patr3s/-737-800-Captain-MIP/CAD/DU_bezel_v3/exports/737-MIP-001_DU-bezel-light-base_v3.stl

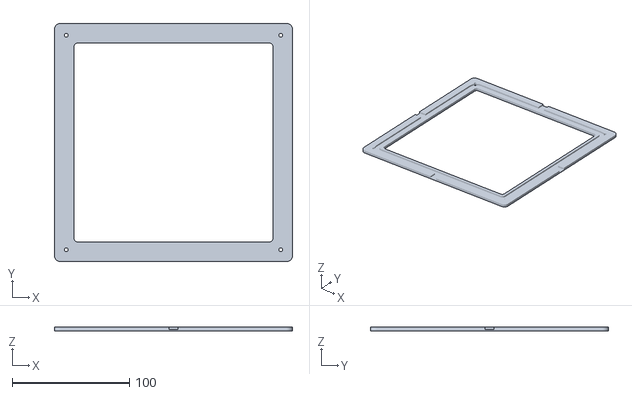
[picture p15: CAD file, 2026-08-28]
CAD/DU_bezel_v3/exports/737-MIP-001_DU-bezel-light-base_v3.stl
203.2 x 203.2 x 3.20
