patr3s/-737-800-Captain-MIP/CAD/Dual_concentric_knob_v1/exports/737-MIP-KNB-002_upper-knob_PROVISIONAL_v1.stl

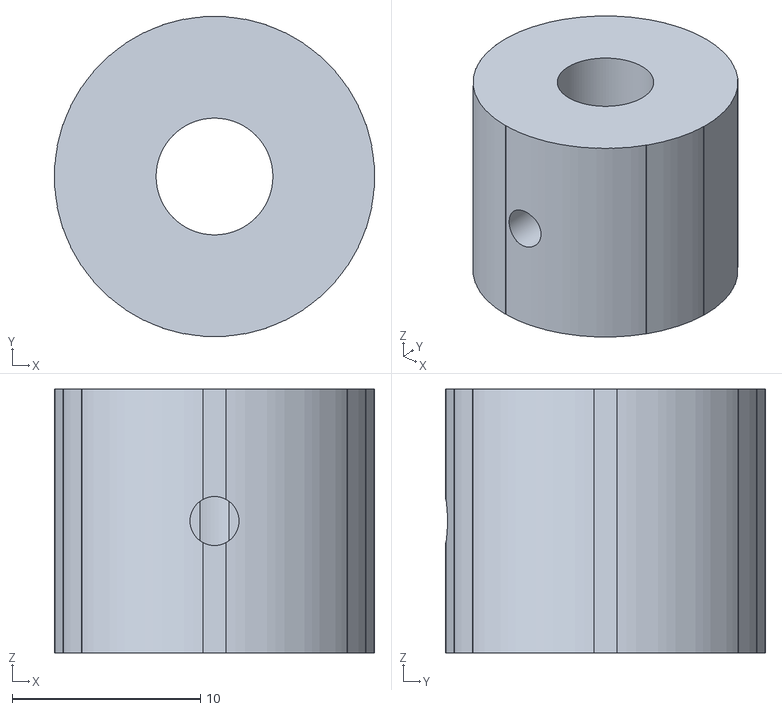
[picture p16: CAD file, 2026-08-28]
CAD/Dual_concentric_knob_v1/exports/737-MIP-KNB-002_upper-knob_PROVISIONAL_v1.stl
17.0 x 17.0 x 14.0
