patr3s/-737-800-Captain-MIP/CAD/PFD_ND_alignment_fit_check_v1/exports_v1.1/737-MIP-CAL-003B_fascia-seam-joiner_v1.1.stl

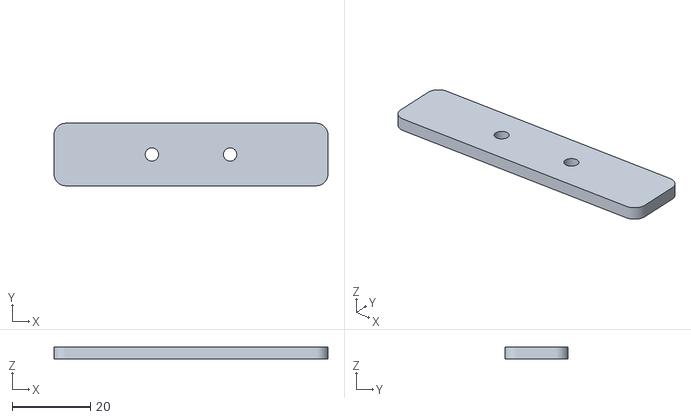
[picture p17: CAD file, 2026-09-04]
CAD/PFD_ND_alignment_fit_check_v1/exports_v1.1/737-MIP-CAL-003B_fascia-seam-joiner_v1.1.stl
70.0 x 16.0 x 3.00
