patr3s/-737-800-Captain-MIP/CAD/Steel_VESA_alignment_interface_v1/exports/737-MIP-007_xy_plate_PROVISIONAL_v1.stl

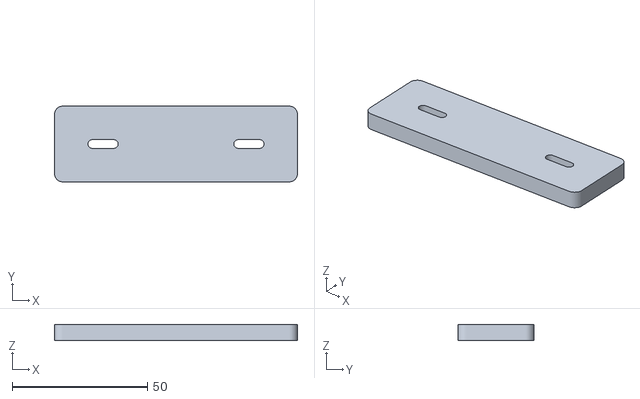
[picture p19: CAD file, 2026-08-28]
CAD/Steel_VESA_alignment_interface_v1/exports/737-MIP-007_xy_plate_PROVISIONAL_v1.stl
90.0 x 28.0 x 6.00
