patr3s/-737-800-Captain-MIP/Ready-to-Print/PFD-ND-Alignment-Fit-Check-v1/737-MIP-CAL-003_carrier_right_v1.stl

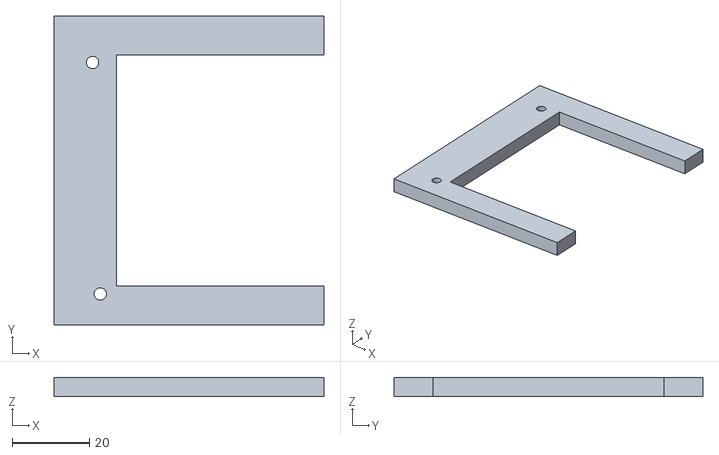
[picture p20: CAD file, 2026-08-28]
Ready-to-Print/PFD-ND-Alignment-Fit-Check-v1/737-MIP-CAL-003_carrier_right_v1.stl
70.0 x 80.0 x 5.00
