patr3s/-737-800-Captain-MIP/CAD/Backlight_test_panel_v1/exports/737-MIP-CAL-002B_backlight-diffuser_v1.1.stl

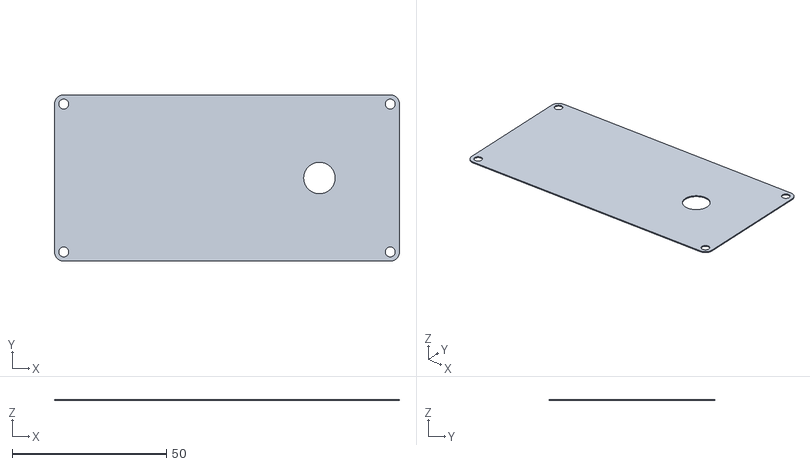
[picture p21: CAD file, 2026-08-28]
CAD/Backlight_test_panel_v1/exports/737-MIP-CAL-002B_backlight-diffuser_v1.1.stl
112.0 x 54.0 x 0.4
