patr3s/-737-800-Captain-MIP/CAD/Backlight_test_panel_v1/exports_multicolor_v1/737-MIP-CAL-004_legends-A-1.0mm.stl

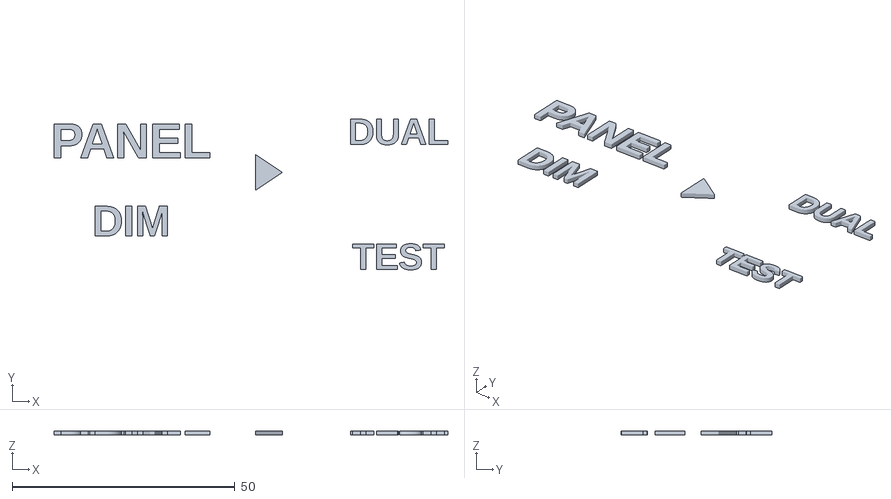
[picture p22: CAD file, 2026-09-04]
CAD/Backlight_test_panel_v1/exports_multicolor_v1/737-MIP-CAL-004_legends-A-1.0mm.stl
88.4 x 33.9 x 1.00
