patr3s/-737-800-Captain-MIP/CAD/BenQ_VESA_cradle_v1/exports/737-MIP-005_VESA-plate_v1.stl

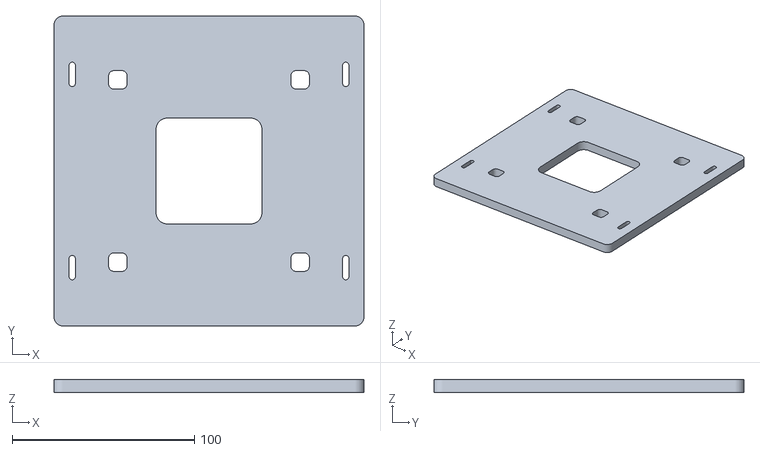
[picture p23: CAD file, 2026-08-27]
CAD/BenQ_VESA_cradle_v1/exports/737-MIP-005_VESA-plate_v1.stl
170.0 x 170.0 x 7.00
