patr3s/-737-800-Captain-MIP/CAD/PFD_ND_carrier_v1/exports/737-MIP-003A_joiner-v1.stl

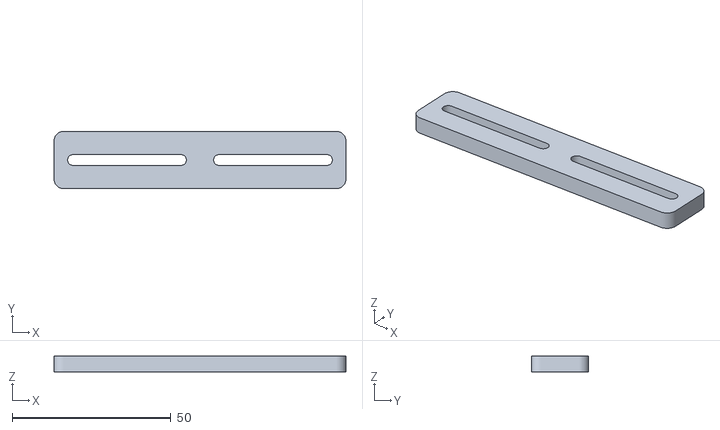
[picture p25: CAD file, 2026-08-27]
CAD/PFD_ND_carrier_v1/exports/737-MIP-003A_joiner-v1.stl
92.0 x 18.0 x 5.00
