patr3s/-737-800-Captain-MIP/CAD/Steel_VESA_alignment_interface_v1/exports/737-MIP-007_shim_20_PROVISIONAL_v1.stl

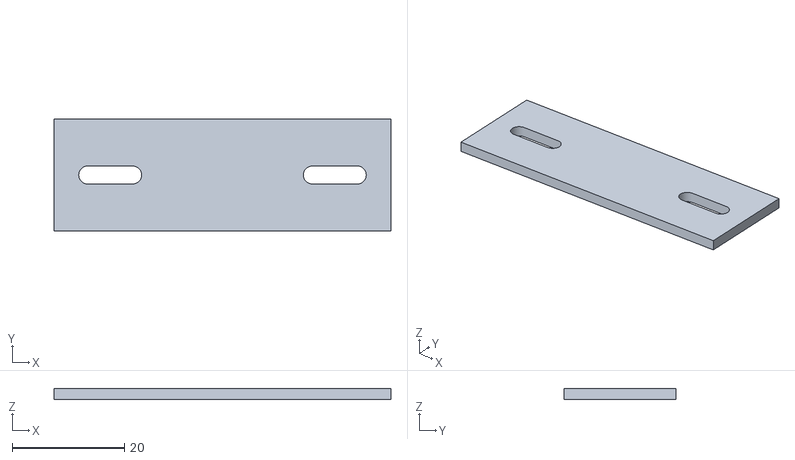
[picture p27: CAD file, 2026-08-28]
CAD/Steel_VESA_alignment_interface_v1/exports/737-MIP-007_shim_20_PROVISIONAL_v1.stl
60.0 x 20.0 x 2.00
