patr3s/-737-800-Captain-MIP/Ready-to-Print/PFD-ND-Alignment-Fit-Check-v1/737-MIP-CAL-003_fascia_seam_left_v1.stl

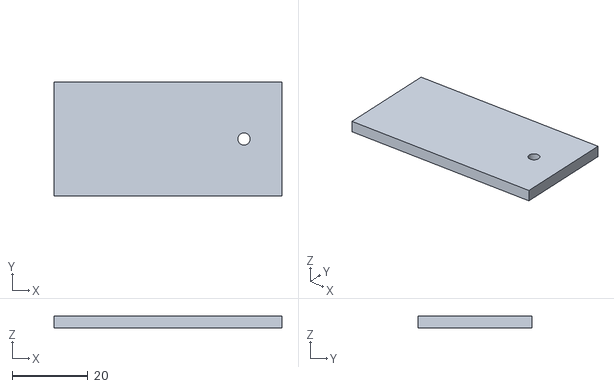
[picture p28: CAD file, 2026-08-28]
Ready-to-Print/PFD-ND-Alignment-Fit-Check-v1/737-MIP-CAL-003_fascia_seam_left_v1.stl
60.0 x 30.0 x 3.20
