patr3s/-737-800-Captain-MIP/CAD/BenQ_VESA_cradle_v1/exports/737-MIP-005A_rear-wing_v1.stl

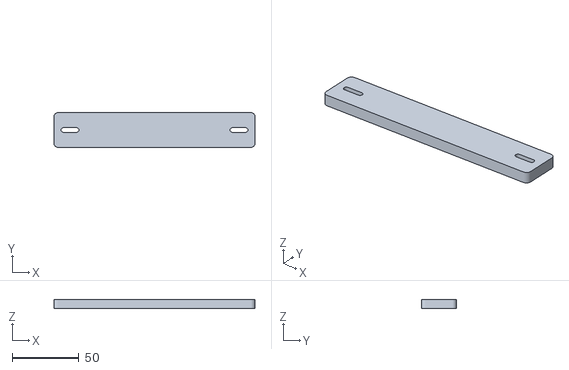
[picture p29: CAD file, 2026-08-27]
CAD/BenQ_VESA_cradle_v1/exports/737-MIP-005A_rear-wing_v1.stl
150.0 x 26.0 x 7.00
