patr3s/-737-800-Captain-MIP/CAD/PFD_ND_carrier_v1/exports/737-MIP-003B_top-interface-v1.stl

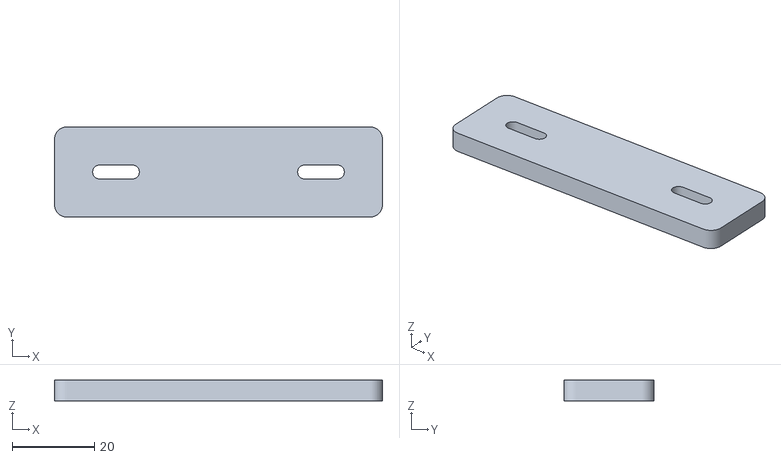
[picture p30: CAD file, 2026-08-27]
CAD/PFD_ND_carrier_v1/exports/737-MIP-003B_top-interface-v1.stl
80.0 x 22.0 x 5.00
