patr3s/-737-800-Captain-MIP/CAD/PFD_ND_fascia_v1/exports/737-MIP-006_bottom_left_base_v1.stl

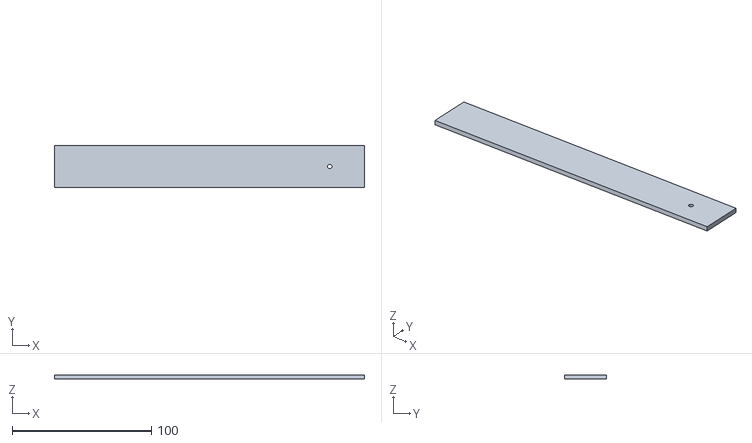
[picture p35: CAD file, 2026-08-28]
CAD/PFD_ND_fascia_v1/exports/737-MIP-006_bottom_left_base_v1.stl
222.5 x 30.2 x 3.20
