patr3s/-737-800-Captain-MIP/Ready-to-Print/PFD-ND-Alignment-Fit-Check-v1/737-MIP-CAL-003_bezel_left_v1.stl

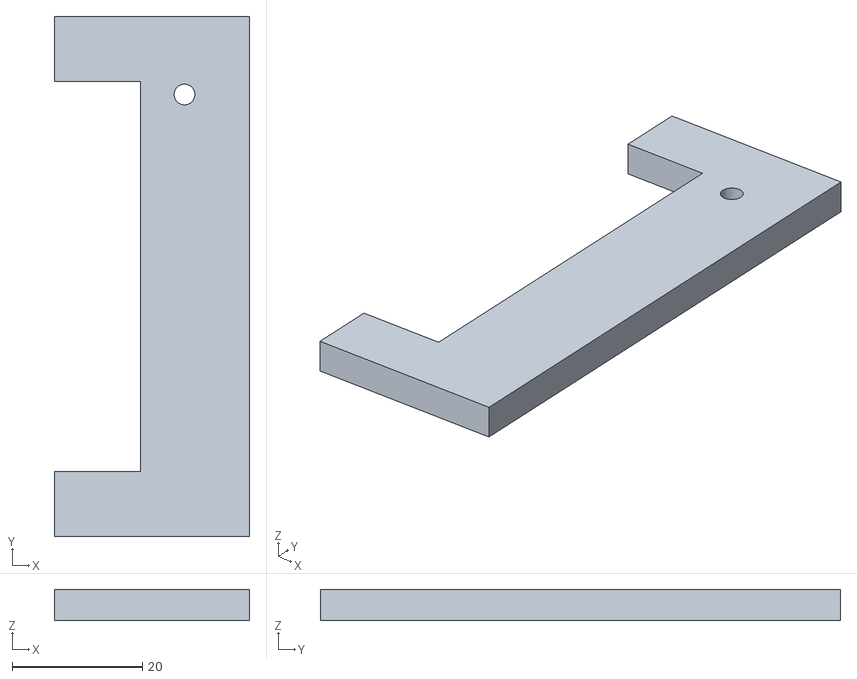
[picture p36: CAD file, 2026-08-28]
Ready-to-Print/PFD-ND-Alignment-Fit-Check-v1/737-MIP-CAL-003_bezel_left_v1.stl
30.0 x 80.0 x 4.80
