patr3s/-737-800-Captain-MIP/Ready-to-Print/PFD-ND-Alignment-Fit-Check-v1/737-MIP-CAL-003_fascia_center_v1.stl

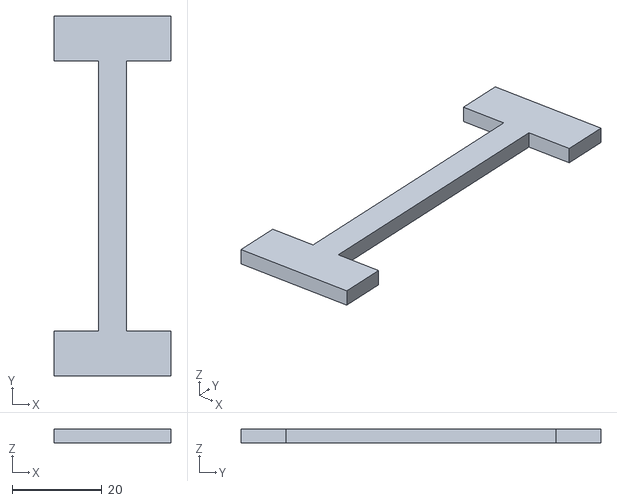
[picture p38: CAD file, 2026-08-28]
Ready-to-Print/PFD-ND-Alignment-Fit-Check-v1/737-MIP-CAL-003_fascia_center_v1.stl
26.0 x 80.0 x 3.20
