patr3s/-737-800-Captain-MIP/CAD/PFD_ND_fascia_v1/exports/737-MIP-006_right_rail_face_v1.stl

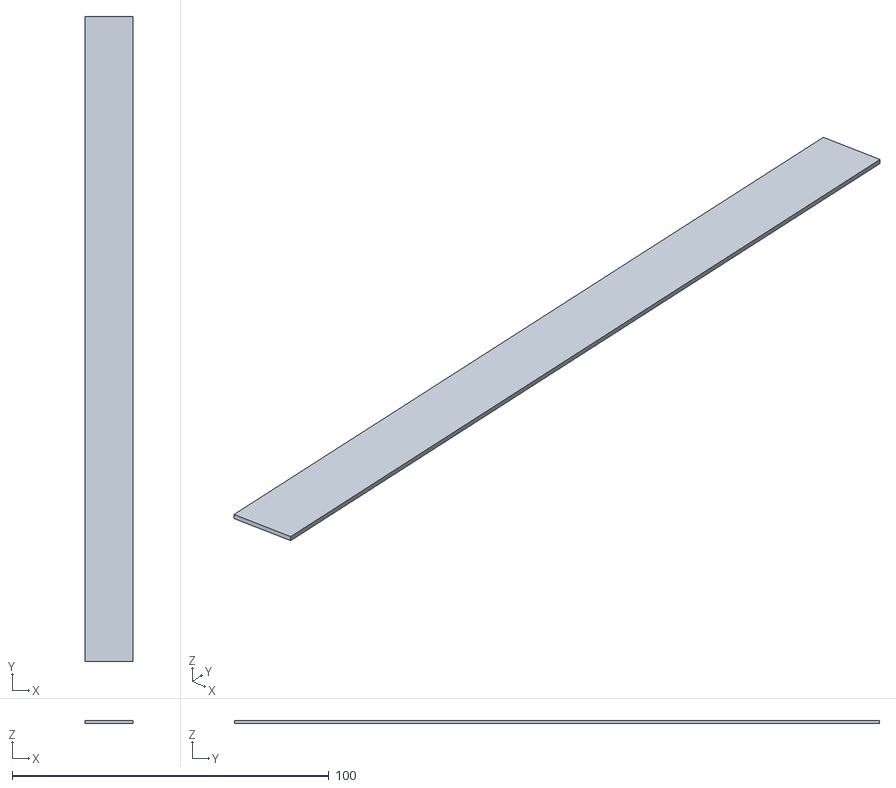
[picture p40: CAD file, 2026-08-28]
CAD/PFD_ND_fascia_v1/exports/737-MIP-006_right_rail_face_v1.stl
15.3 x 203.6 x 1.00
