patr3s/-737-800-Captain-MIP/CAD/PFD_ND_fascia_v1/exports/737-MIP-006_right_rail_base_v1.stl

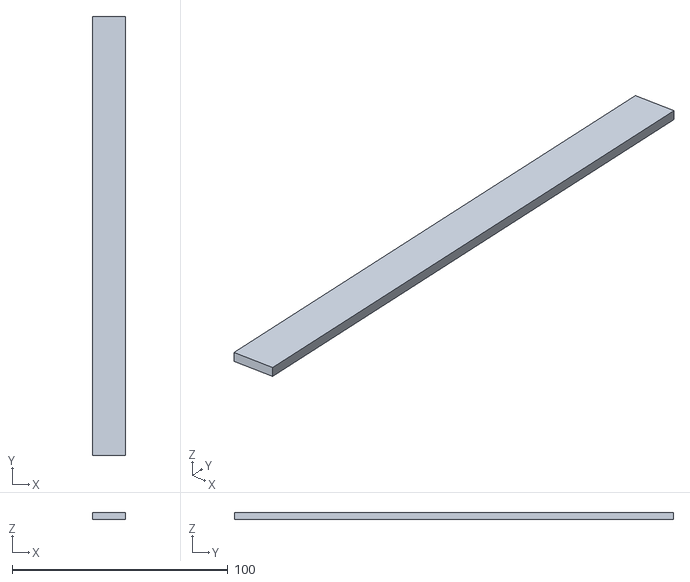
[picture p42: CAD file, 2026-08-28]
CAD/PFD_ND_fascia_v1/exports/737-MIP-006_right_rail_base_v1.stl
15.3 x 203.6 x 3.20
